ett2/autopark/ENGI301/project2/docs/fob_brd1.png

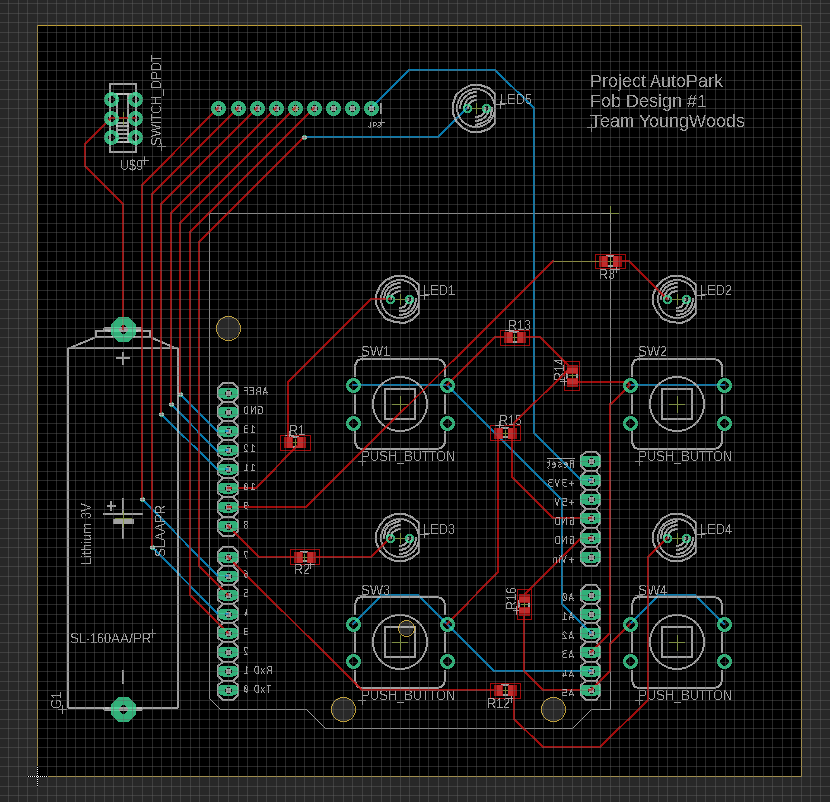
ENGI301/project2/docs/fob_brd1.png
