ett2/autopark/testing/rftest0.ino

/* Radio-specific functions for AutoPark Project */

void send_message() {
  volatile char message = state + '0';
  Serial.println(message);
  rf69.send((uint8_t *)message, 1);
  rf69.waitPacketSent();
  Serial.println("State message sent.");
}


void receive_message() {
  uint8_t buf[RH_RF69_MAX_MESSAGE_LEN];
  uint8_t len = sizeof(buf);

  if (rf69.waitAvailableTimeout(500))  { 
    // Should be a reply message for us now   
    if (rf69.recv(buf, &len)) {
      Serial.print("Got a reply: ");
      Serial.println((char*)buf);
      Blink(LED, 50, 3); //blink LED 3 times, 50ms between blinks
    } else {
      Serial.println("Receive failed");
    }
  } else {
    Serial.println("No reply, is another RFM69 listening?");
  }
}


void radio_reset() {
   // manual reset
  digitalWrite(RFM69_RST, HIGH);
  delay(10);
  digitalWrite(RFM69_RST, LOW);
  delay(10);

  if (!rf69.init()) {
    Serial.println("RFM69 radio init failed");
    while (1);
  }
  Serial.println("RFM69 radio init OK!");
}


void Blink(byte PIN, byte DELAY_MS, byte loops) {
  for (byte i=0; i<loops; i++)  {
    digitalWrite(PIN,HIGH);
    delay(DELAY_MS);
    digitalWrite(PIN,LOW);
    delay(DELAY_MS);
  }
}
